Amrlxyz/esp-lfr-buggy/python-logger/misc/Screenshot 2024-03-25 131633.png

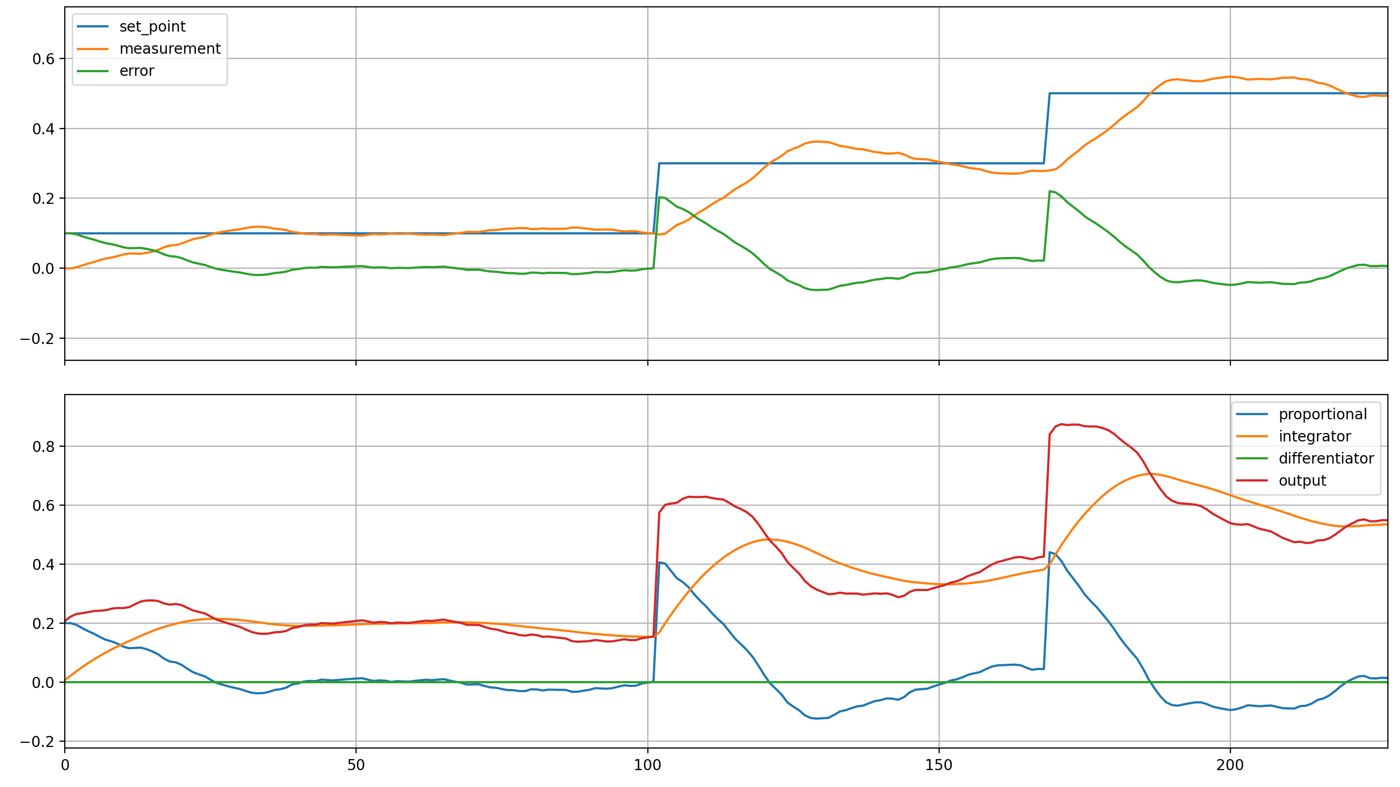
python-logger/misc/Screenshot 2024-03-25 131633.png
