Amrlxyz/esp-lfr-buggy/python-logger/misc/Screenshot 2024-04-28 034905.png

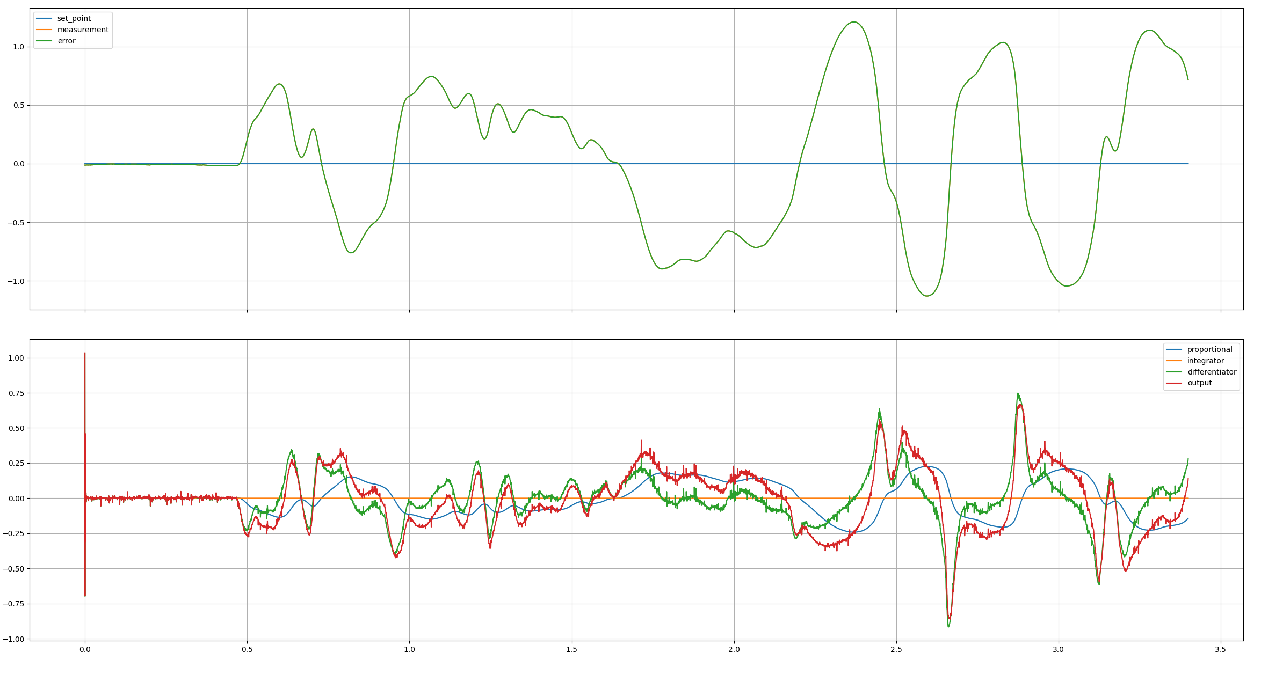
python-logger/misc/Screenshot 2024-04-28 034905.png
