Amrlxyz/esp-lfr-buggy/python-logger/misc/Screenshot 2024-04-29 144606.png

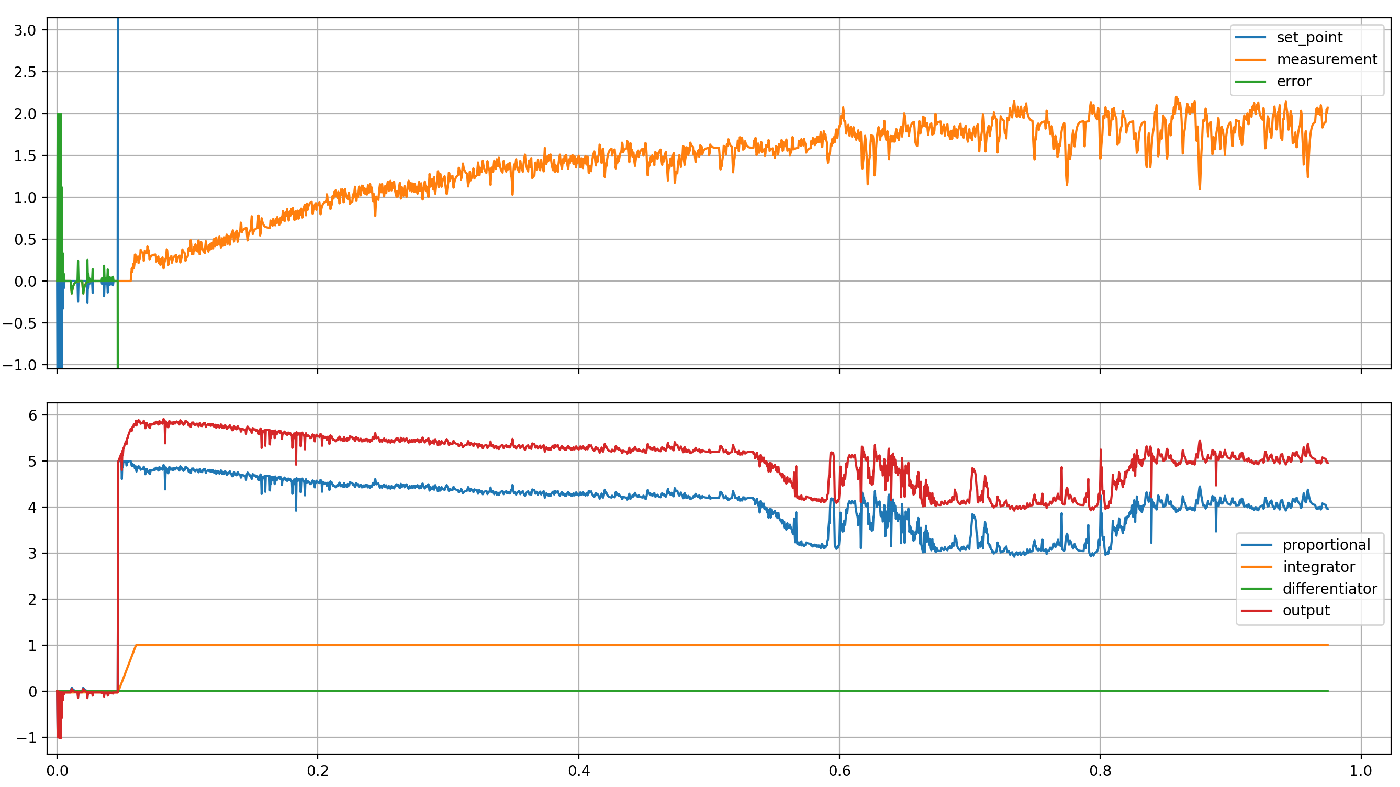
python-logger/misc/Screenshot 2024-04-29 144606.png
