Amrlxyz/esp-lfr-buggy/hardware/Buggy CAD/Buggy CAD v3/MOTOR_MODULE_2/input side encoder half.SLDPRT

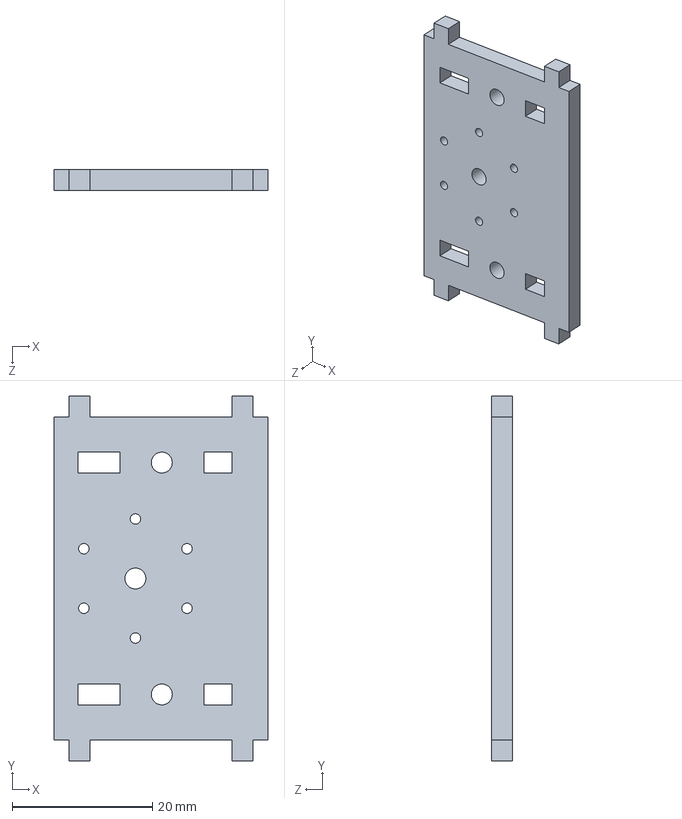
[picture p32: CAD file, 2025-04-30]
hardware/Buggy CAD/Buggy CAD v3/MOTOR_MODULE_2/input side encoder half.SLDPRT
30.5 x 52.1 x 3.00 mm
