Amrlxyz/esp-lfr-buggy/hardware/Buggy CAD/Buggy CAD v3/Printed/30_deg_ramp.STEP

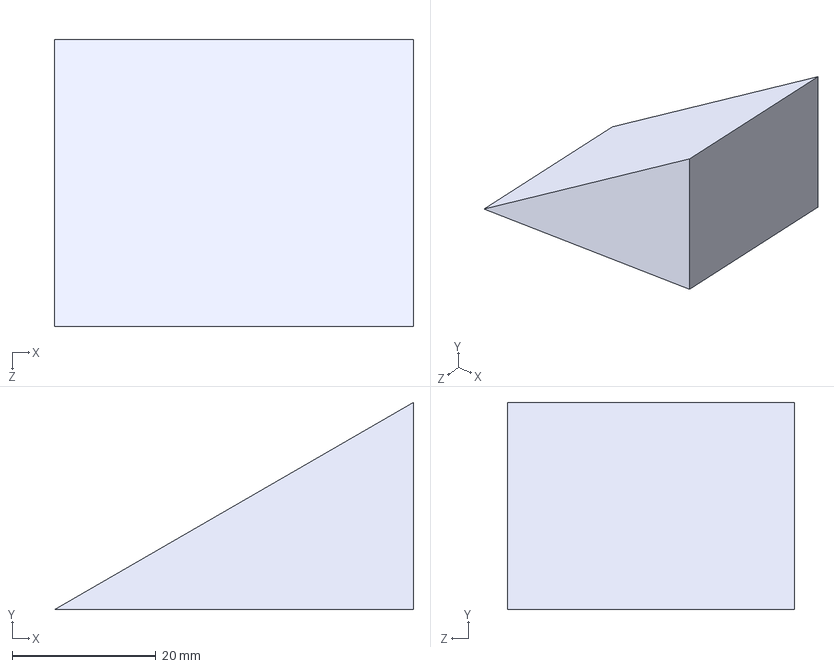
[picture p33: CAD file, 2025-04-30]
hardware/Buggy CAD/Buggy CAD v3/Printed/30_deg_ramp.STEP
50.0 x 28.9 x 40.0 mm
