Amrlxyz/esp-lfr-buggy/hardware/Buggy CAD/Buggy CAD v3/5mm M3 Standoffs.SLDPRT

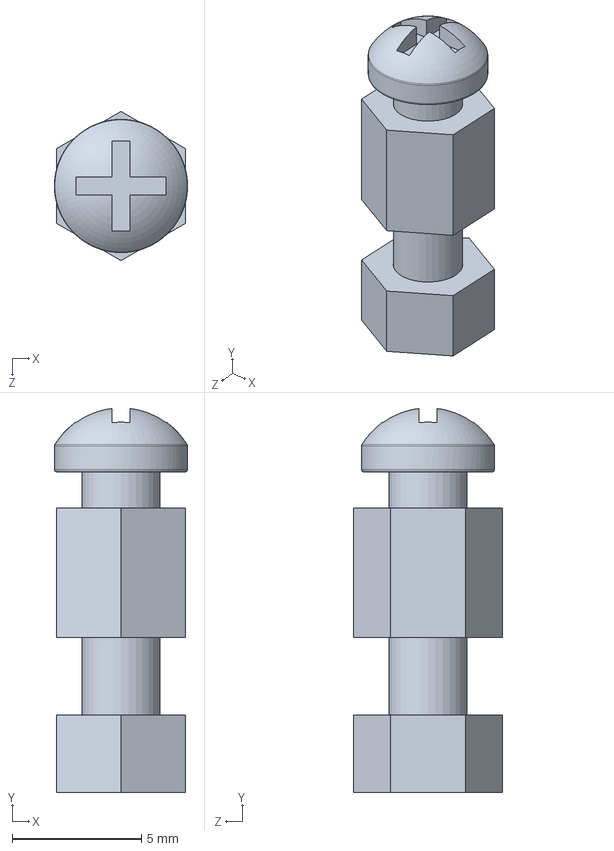
[picture p34: CAD file, 2025-04-30]
hardware/Buggy CAD/Buggy CAD v3/5mm M3 Standoffs.SLDPRT
5.16 x 14.9 x 5.77 mm
