Amrlxyz/esp-lfr-buggy/hardware/Buggy CAD/Buggy CAD v3/MOTOR_MODULE_2/longnut.SLDPRT

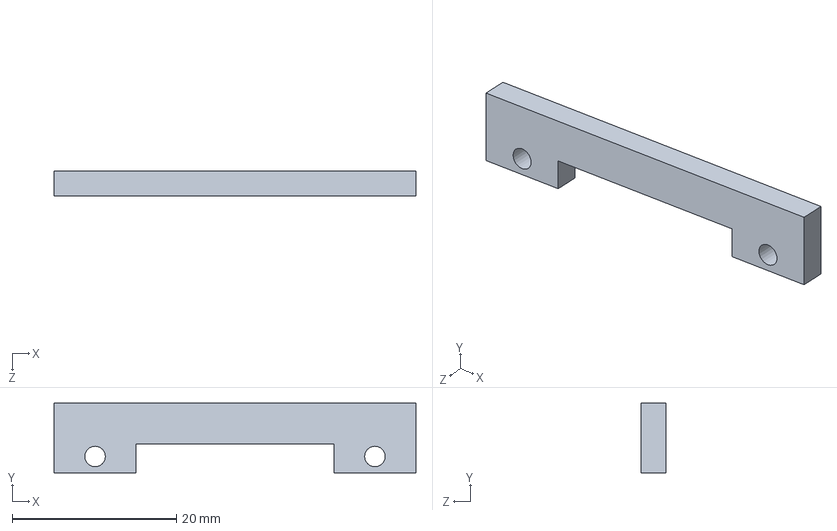
[picture p35: CAD file, 2025-04-30]
hardware/Buggy CAD/Buggy CAD v3/MOTOR_MODULE_2/longnut.SLDPRT
44.1 x 8.50 x 3.00 mm
