Amrlxyz/esp-lfr-buggy/hardware/Buggy CAD/Buggy CAD v3/Castor_Assembly/Rod.SLDPRT

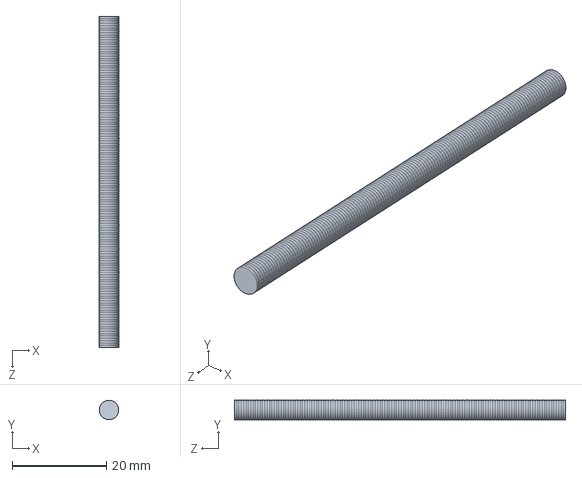
[picture p36: CAD file, 2025-04-30]
hardware/Buggy CAD/Buggy CAD v3/Castor_Assembly/Rod.SLDPRT
4.15 x 4.15 x 70.4 mm
