Amrlxyz/esp-lfr-buggy/hardware/Buggy CAD/Buggy CAD v3/MOTOR_MODULE_2/output_axle.SLDPRT

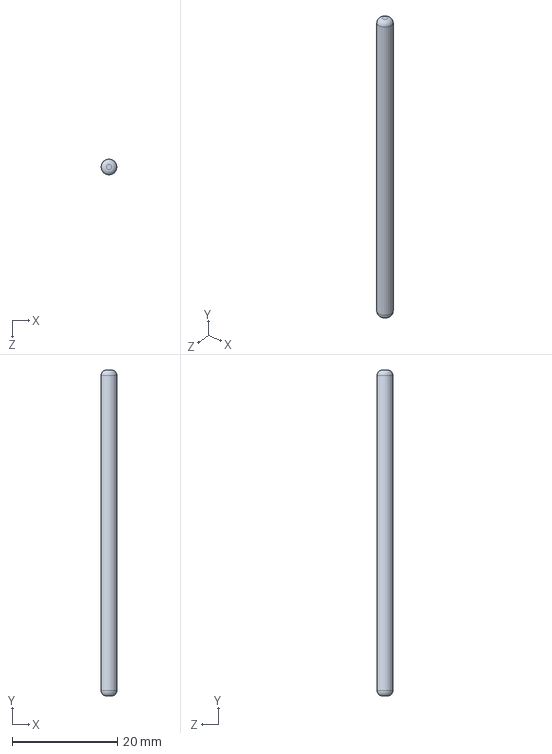
[picture p37: CAD file, 2025-04-30]
hardware/Buggy CAD/Buggy CAD v3/MOTOR_MODULE_2/output_axle.SLDPRT
3.00 x 62.0 x 3.00 mm
