Amrlxyz/esp-lfr-buggy/hardware/Buggy CAD/Buggy CAD v3/Castor_Assembly/Ball.SLDPRT

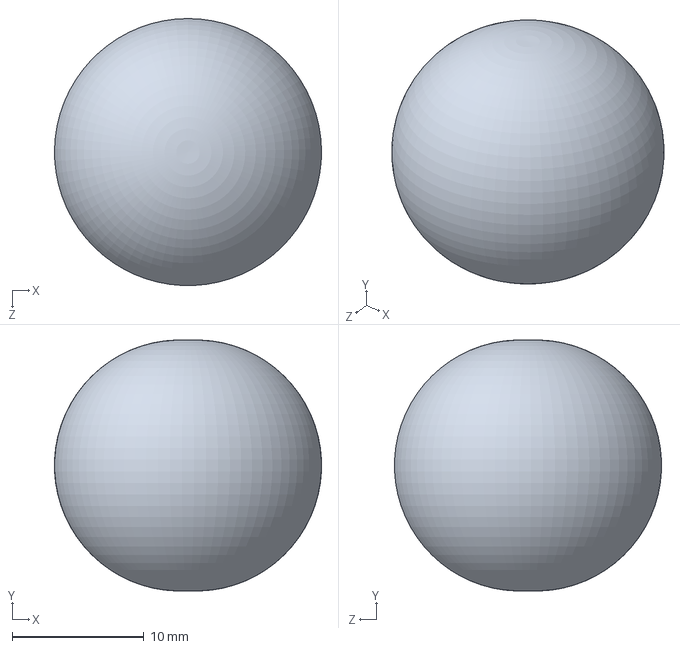
[picture p39: CAD file, 2025-04-30]
hardware/Buggy CAD/Buggy CAD v3/Castor_Assembly/Ball.SLDPRT
20.2 x 19.0 x 20.2 mm
