Amrlxyz/esp-lfr-buggy/hardware/Buggy CAD/Buggy CAD v3/MOTOR_MODULE_2/input side motor half.SLDPRT

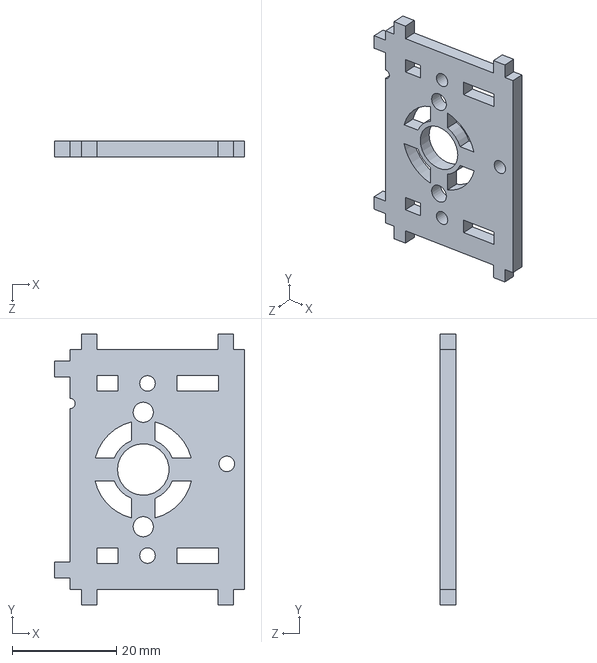
[picture p40: CAD file, 2025-04-30]
hardware/Buggy CAD/Buggy CAD v3/MOTOR_MODULE_2/input side motor half.SLDPRT
36.6 x 52.1 x 3.00 mm
