Amrlxyz/esp-lfr-buggy/hardware/Buggy CAD/Buggy CAD v3/Castor_Assembly/Ball Housing.SLDPRT

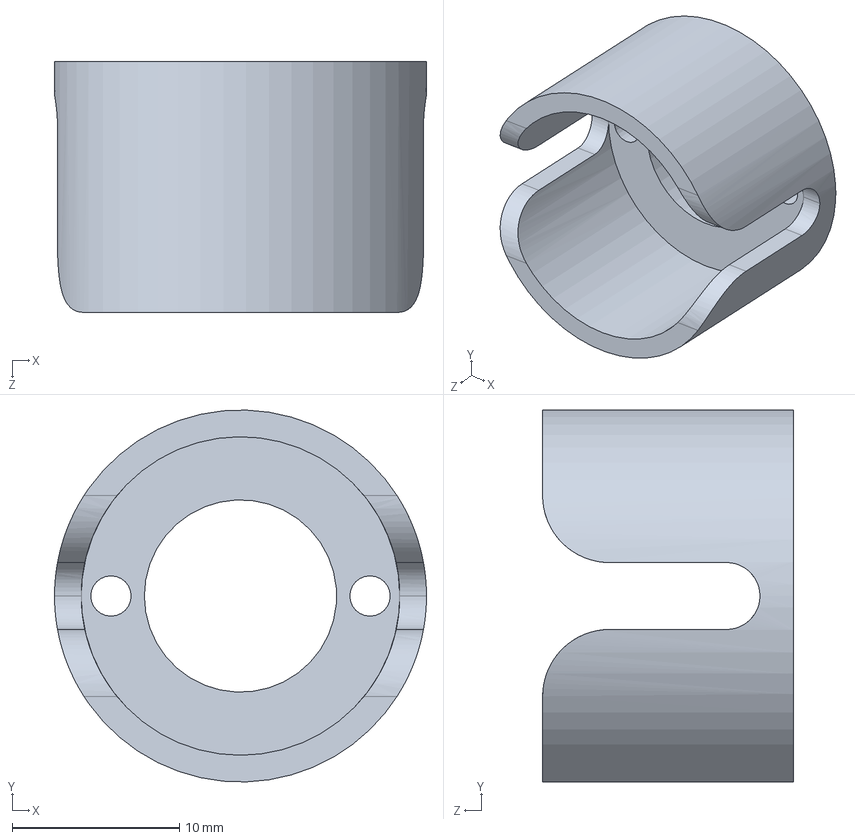
[picture p41: CAD file, 2025-04-30]
hardware/Buggy CAD/Buggy CAD v3/Castor_Assembly/Ball Housing.SLDPRT
22.2 x 22.2 x 15.0 mm
