Amrlxyz/esp-lfr-buggy/hardware/Buggy CAD/Buggy CAD v3/MOTOR_MODULE_2/Gear - 16.SLDPRT

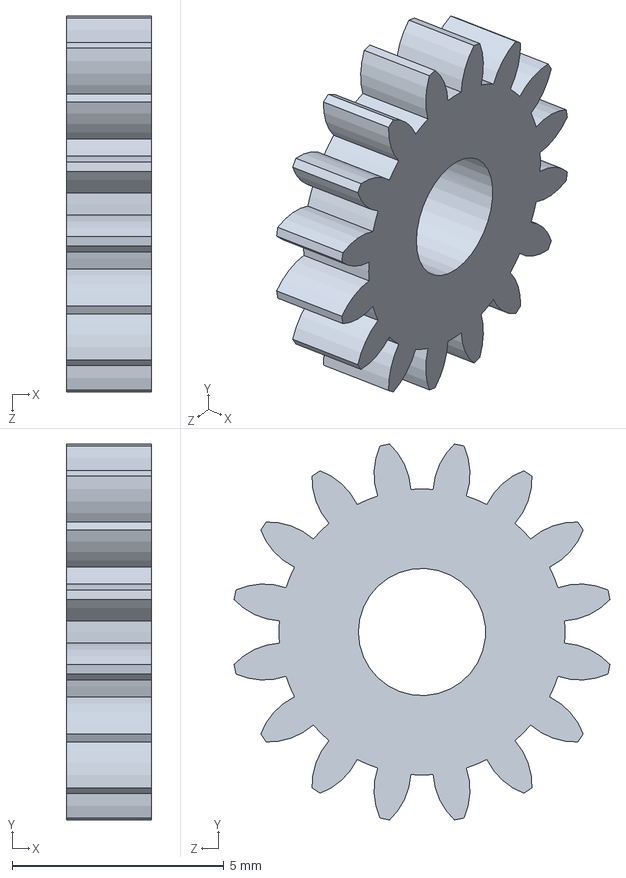
[picture p42: CAD file, 2025-04-30]
hardware/Buggy CAD/Buggy CAD v3/MOTOR_MODULE_2/Gear - 16.SLDPRT
2.00 x 8.87 x 8.87 mm
