Amrlxyz/esp-lfr-buggy/hardware/Buggy CAD/Buggy CAD v3/MOTOR_MODULE_2/conn plate.SLDPRT

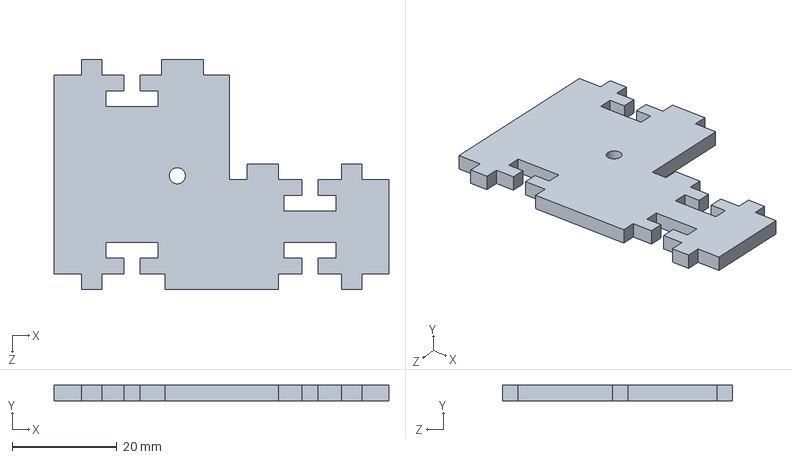
[picture p43: CAD file, 2025-04-30]
hardware/Buggy CAD/Buggy CAD v3/MOTOR_MODULE_2/conn plate.SLDPRT
64.1 x 3.00 x 44.0 mm
