Amrlxyz/esp-lfr-buggy/hardware/Buggy CAD/Buggy CAD v3/MOTOR_MODULE_2/Gear - 50_10(1).SLDPRT

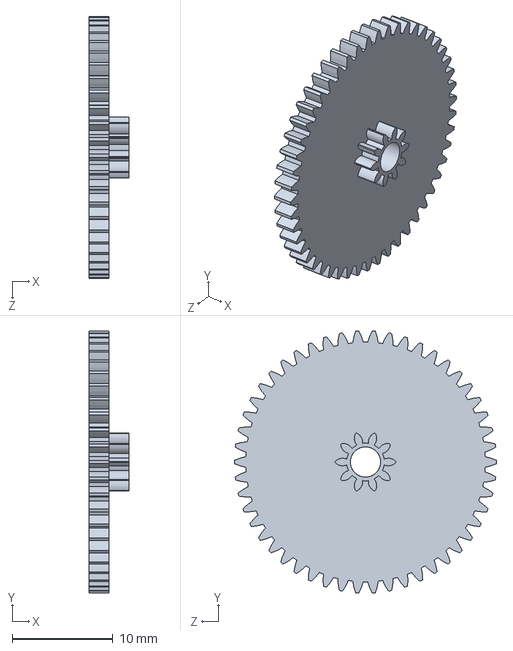
[picture p44: CAD file, 2025-04-30]
hardware/Buggy CAD/Buggy CAD v3/MOTOR_MODULE_2/Gear - 50_10(1).SLDPRT
4.00 x 26.0 x 26.0 mm
