Amrlxyz/esp-lfr-buggy/hardware/Buggy CAD/Buggy CAD v3/30mm M3 Standoffs.SLDPRT

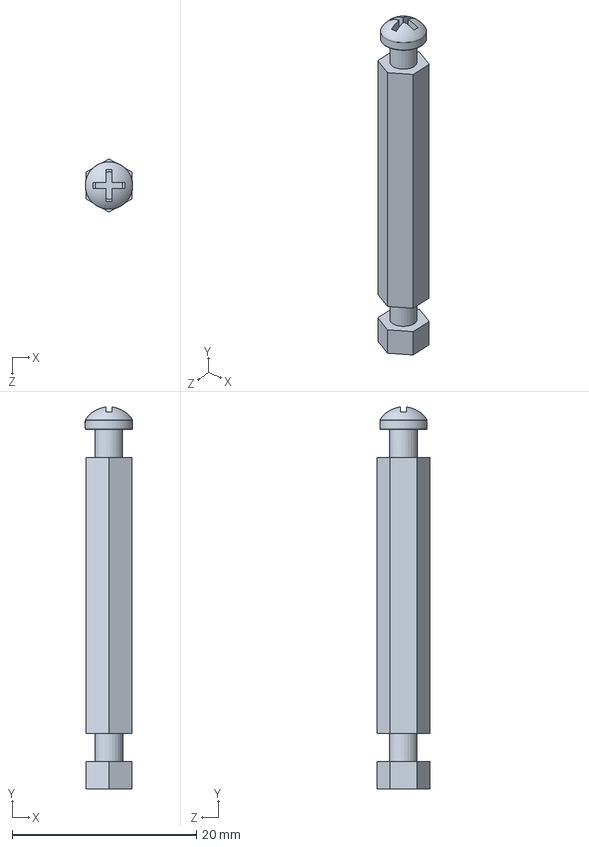
[picture p45: CAD file, 2025-04-30]
hardware/Buggy CAD/Buggy CAD v3/30mm M3 Standoffs.SLDPRT
5.16 x 41.5 x 5.77 mm
