Amrlxyz/esp-lfr-buggy/hardware/Buggy CAD/Buggy CAD v3/MOTOR_MODULE_2/ENCODER.SLDPRT

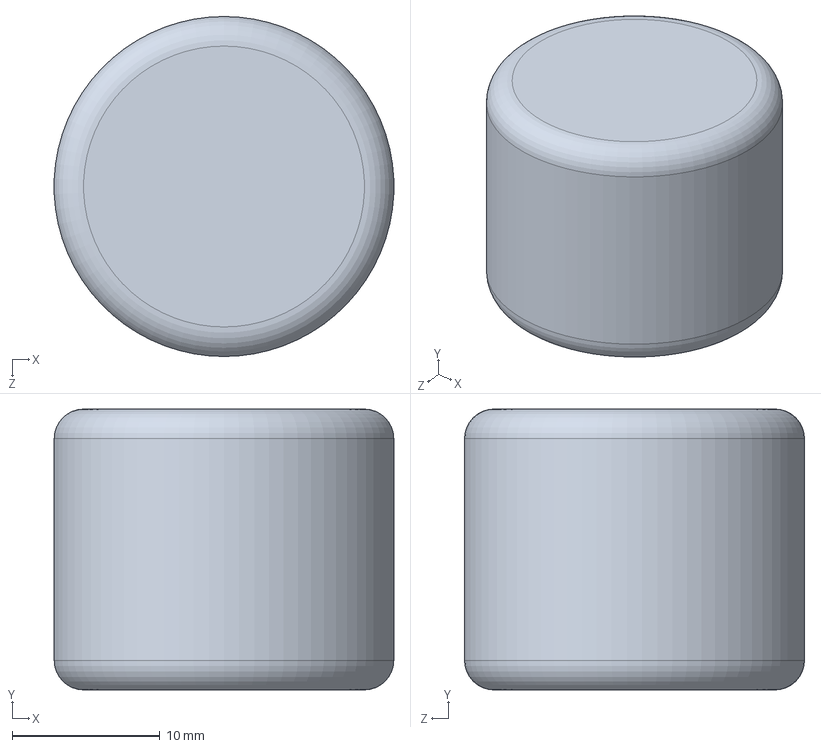
[picture p46: CAD file, 2025-04-30]
hardware/Buggy CAD/Buggy CAD v3/MOTOR_MODULE_2/ENCODER.SLDPRT
23.0 x 19.0 x 23.0 mm
