Amrlxyz/esp-lfr-buggy/hardware/Buggy CAD/Buggy CAD v3/MOTOR_MODULE_2/shortnut.SLDPRT

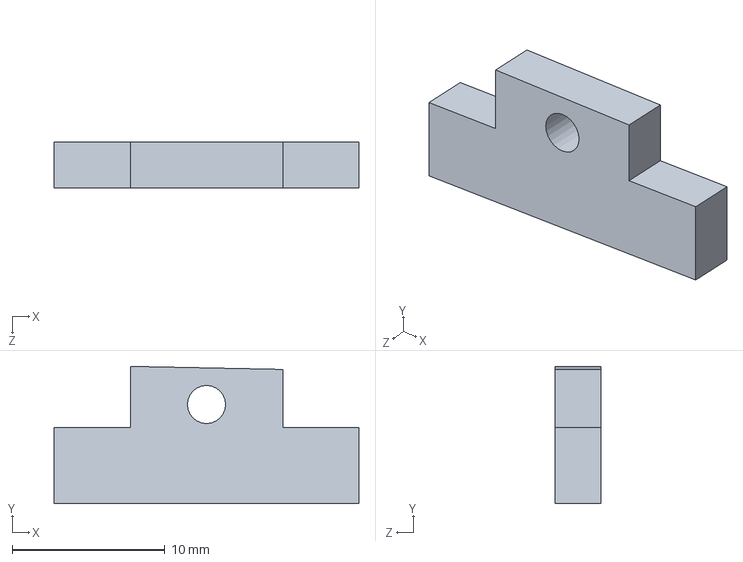
[picture p47: CAD file, 2025-04-30]
hardware/Buggy CAD/Buggy CAD v3/MOTOR_MODULE_2/shortnut.SLDPRT
20.0 x 9.00 x 3.00 mm
