Amrlxyz/esp-lfr-buggy/hardware/Buggy CAD/Buggy CAD v3/Wheel_Nut(1).SLDPRT

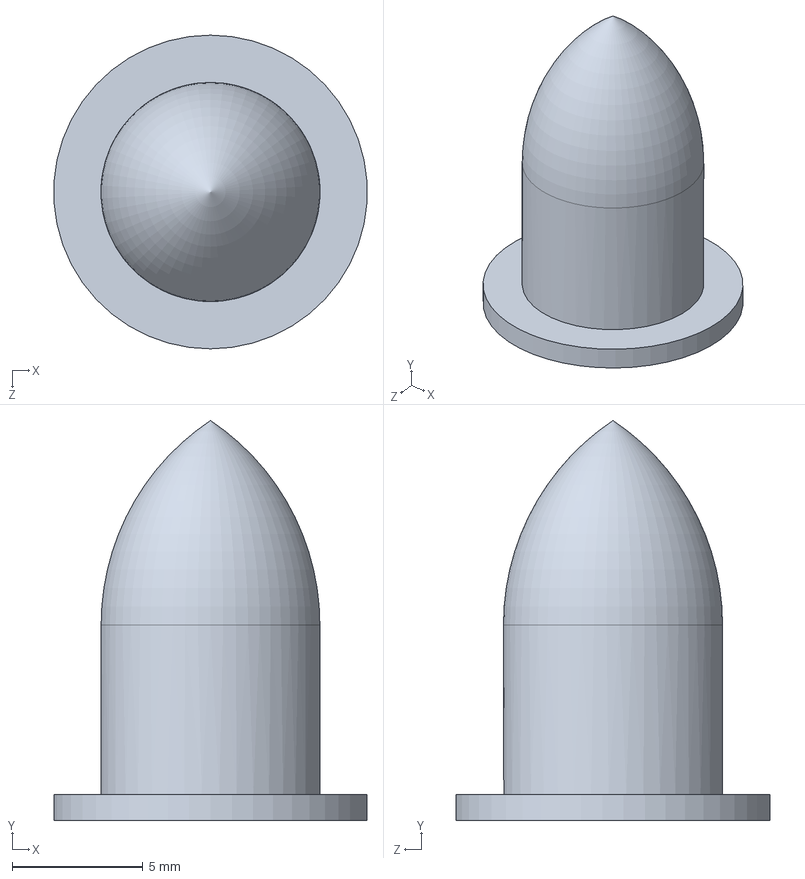
[picture p48: CAD file, 2025-04-30]
hardware/Buggy CAD/Buggy CAD v3/Wheel_Nut(1).SLDPRT
12.0 x 15.3 x 12.0 mm
