Amrlxyz/esp-lfr-buggy/hardware/Buggy CAD/Buggy CAD v3/Group_48.DXF

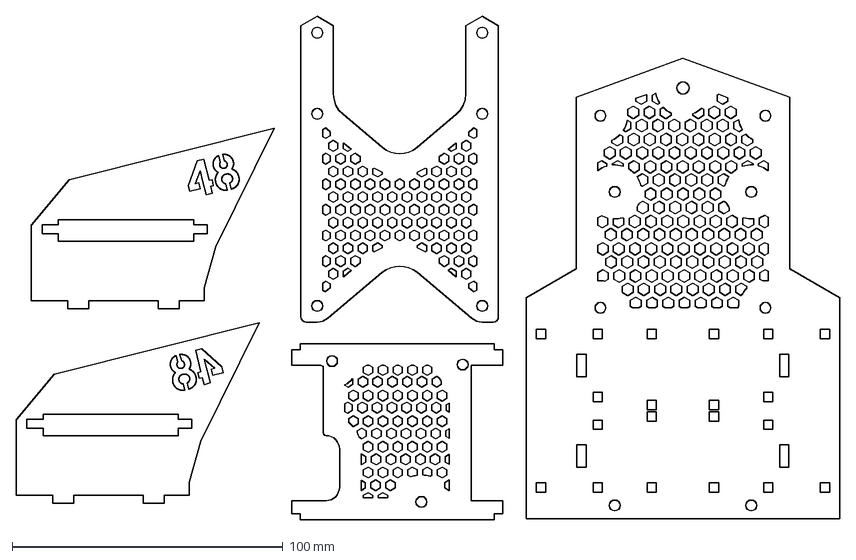
[picture p49: CAD file, 2025-04-30]
hardware/Buggy CAD/Buggy CAD v3/Group_48.DXF
304.5 x 186.0 mm
