Amrlxyz/esp-lfr-buggy/hardware/Buggy CAD/Buggy CAD v3/MOTOR_MODULE_2/Gear - 48_12(1).SLDPRT

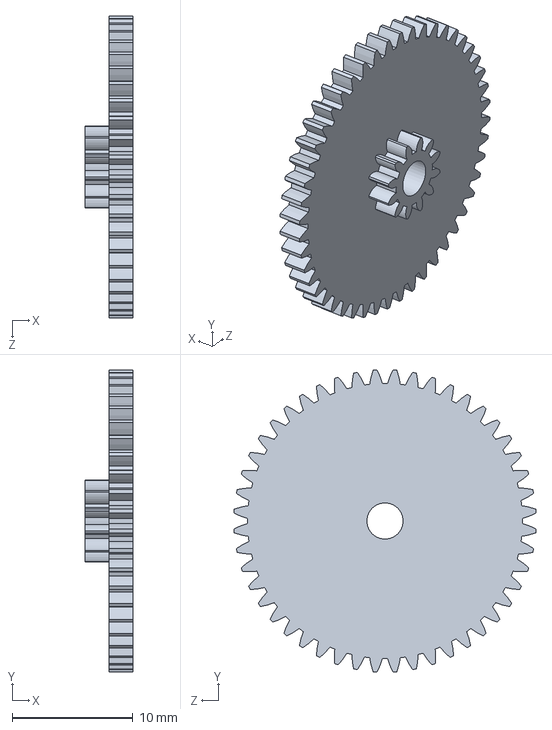
[picture p50: CAD file, 2025-04-30]
hardware/Buggy CAD/Buggy CAD v3/MOTOR_MODULE_2/Gear - 48_12(1).SLDPRT
4.00 x 25.0 x 25.0 mm
