Amrlxyz/esp-lfr-buggy/hardware/Buggy CAD/Buggy CAD v3/MOTOR_MODULE_2/output_side2.SLDPRT

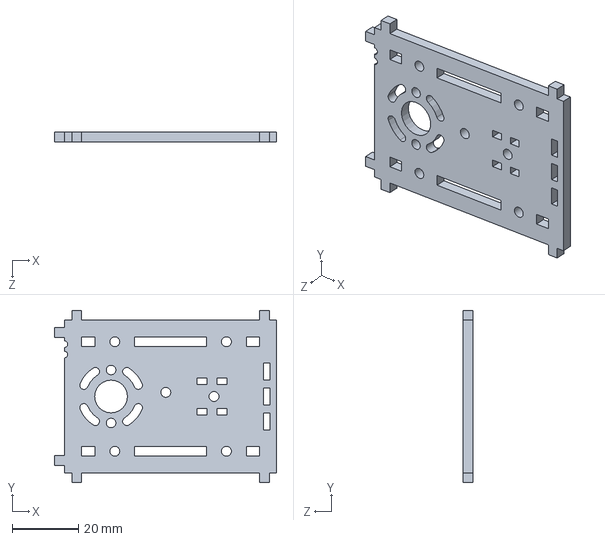
[picture p51: CAD file, 2025-04-30]
hardware/Buggy CAD/Buggy CAD v3/MOTOR_MODULE_2/output_side2.SLDPRT
67.1 x 52.1 x 3.00 mm
