Amrlxyz/esp-lfr-buggy/hardware/Buggy CAD/Buggy CAD v3/MOTOR_MODULE_2/Axle Long.SLDPRT

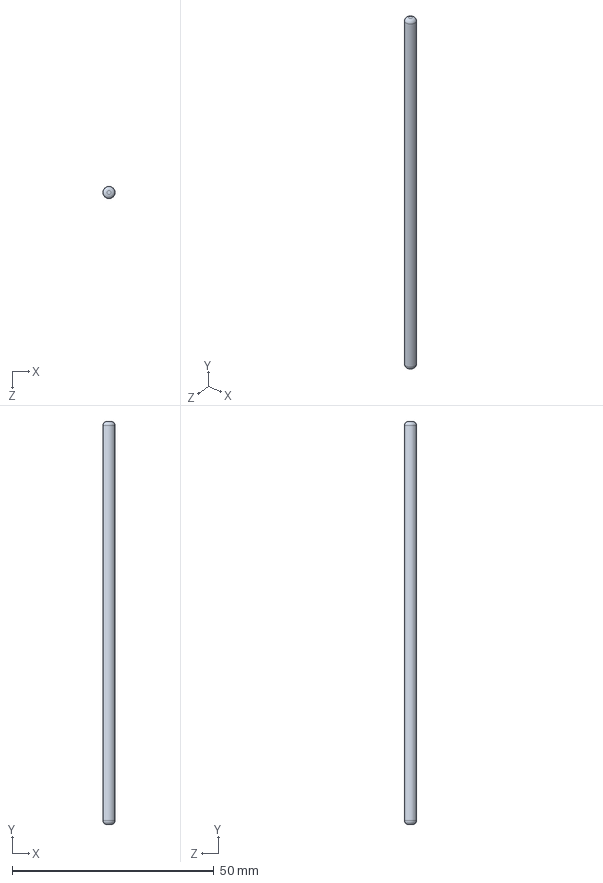
[picture p52: CAD file, 2025-04-30]
hardware/Buggy CAD/Buggy CAD v3/MOTOR_MODULE_2/Axle Long.SLDPRT
3.00 x 100.0 x 2.99 mm
