Amrlxyz/esp-lfr-buggy/hardware/Buggy CAD/Buggy CAD v3/Tyre(1)(1).SLDPRT

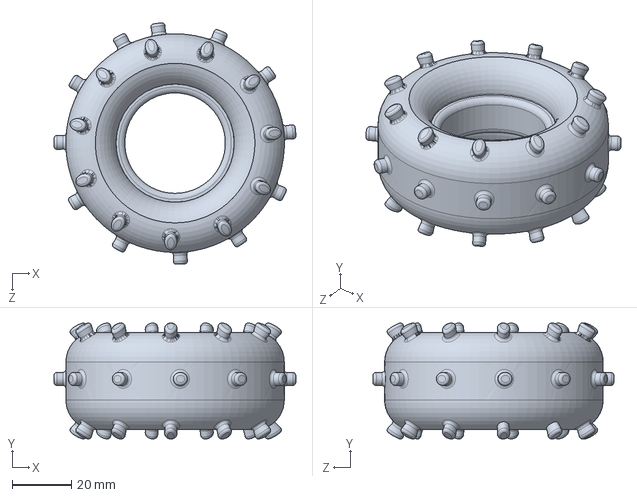
[picture p53: CAD file, 2025-04-30]
hardware/Buggy CAD/Buggy CAD v3/Tyre(1)(1).SLDPRT
81.9 x 39.3 x 81.7 mm
