Amrlxyz/esp-lfr-buggy/include/OneWire_Methods.h

void OneWire_Delay(char letter);
void OneWire_TestDelays(void);
bool OneWire_Reset(void);
void OneWire_WriteBit(bool bit_to_write);
bool OneWire_ReadBit(void);
void OneWire_WriteByte(unsigned char byte_to_write);
unsigned char OneWire_ReadByte(void);
